Youngwer/CASA0022_Dissertation/image/neonDB table.png

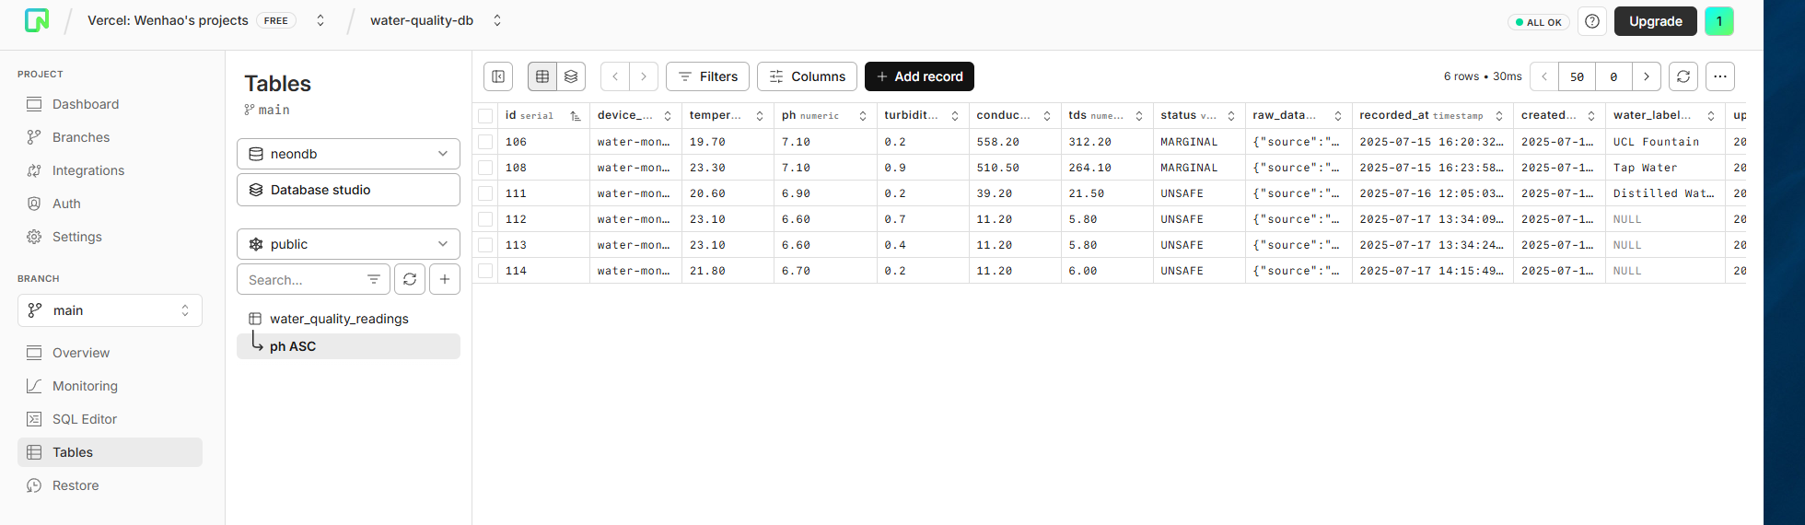
image/neonDB table.png
