Youngwer/CASA0022_Dissertation/image/pH solution.jpg

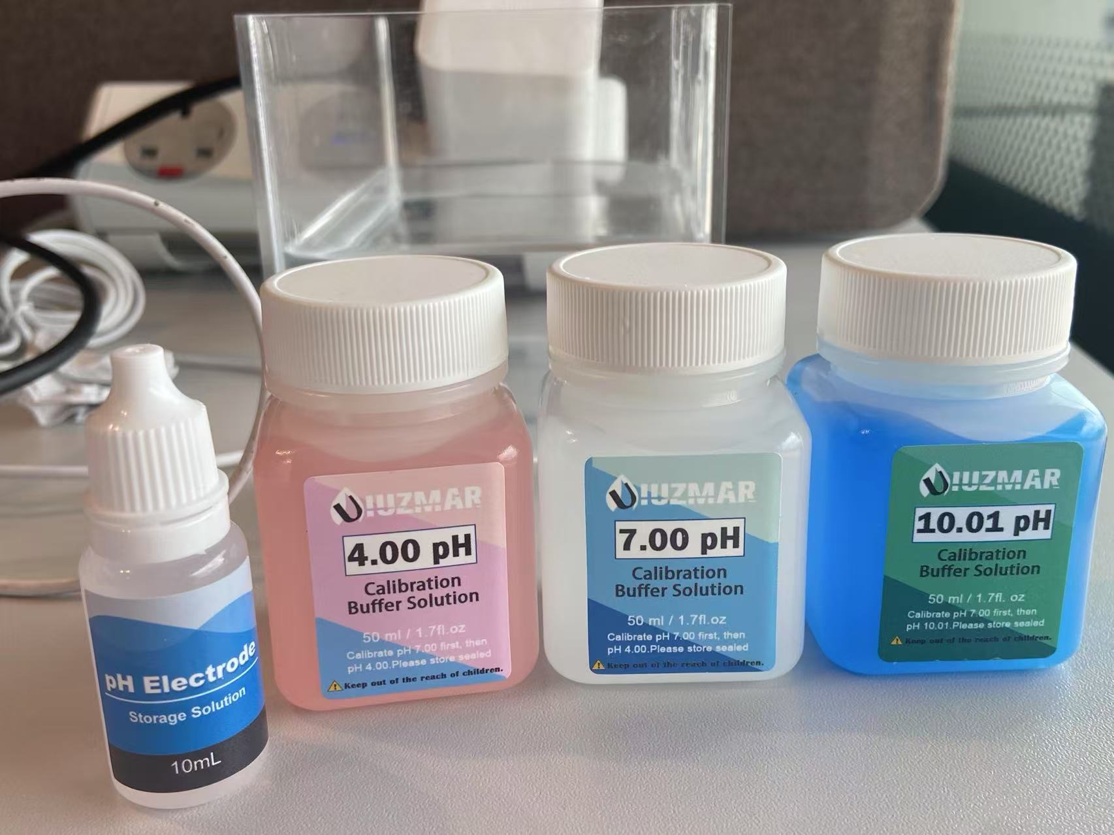
image/pH solution.jpg
