Youngwer/CASA0022_Dissertation/image/web/label choice.png

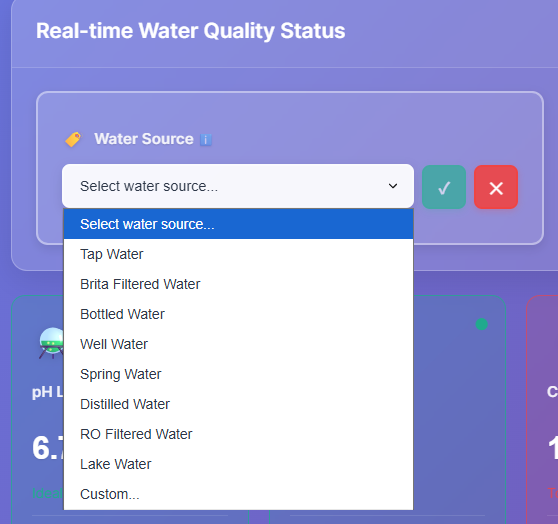
image/web/label choice.png
