Youngwer/CASA0022_Dissertation/image/Wenhao_Yang.png

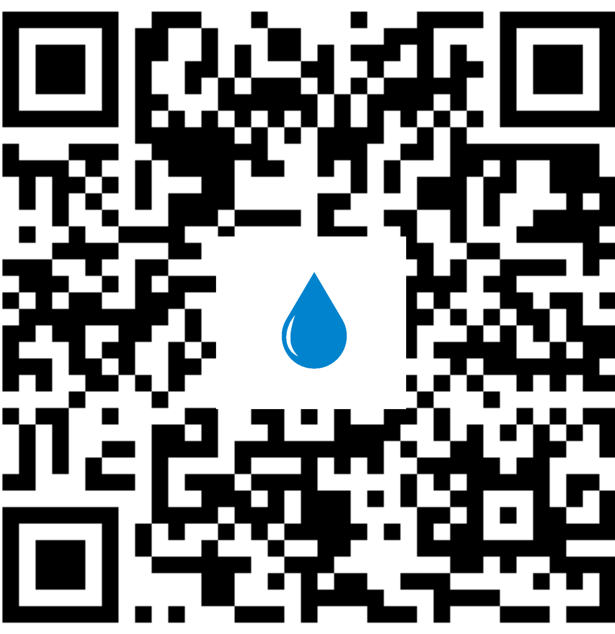
image/Wenhao_Yang.png
