Youngwer/CASA0022_Dissertation/image/Turbidity-calibration.jpg

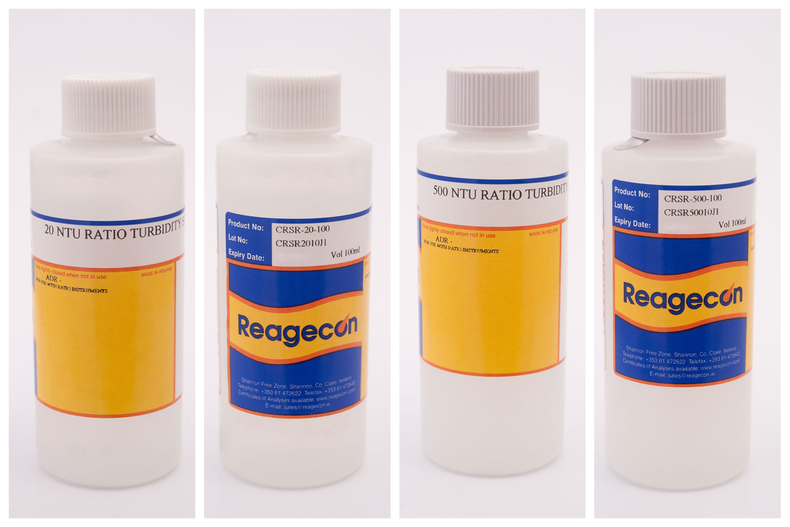
image/Turbidity-calibration.jpg
