Youngwer/CASA0022_Dissertation/image/web/history.png

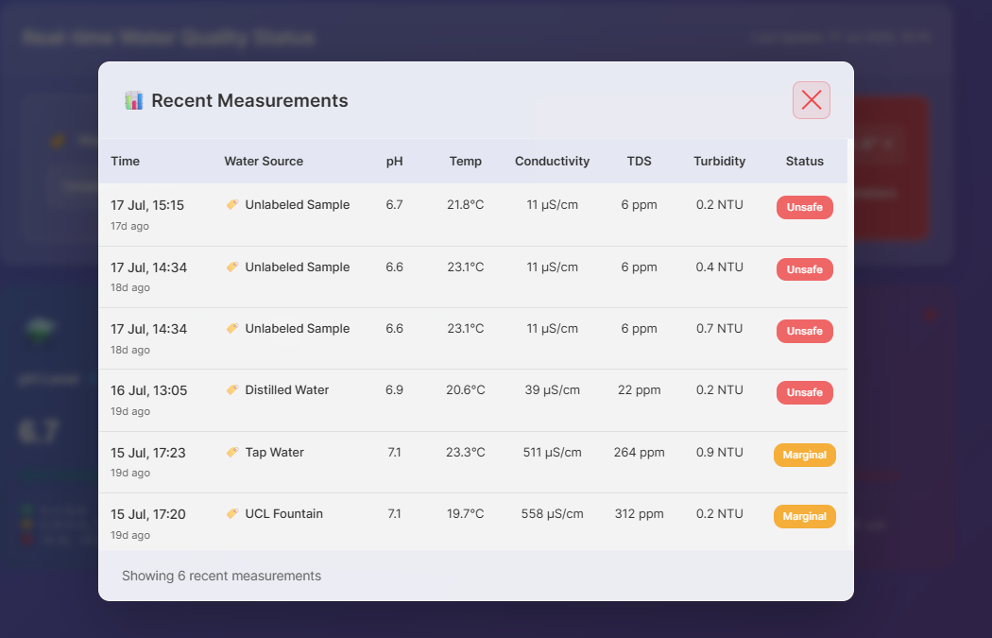
image/web/history.png
