Youngwer/CASA0022_Dissertation/Arduino/test/epaper_test/epdif.h

/**
 *  @filename   :   epdif.h
 *  @brief      :   Header file of epdif.cpp providing EPD interface functions
 *                  Users have to implement all the functions in epdif.cpp
 *  @author     :   Yehui from Waveshare
 *
 *  Copyright (C) Waveshare     August 10 2017
 *
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
 * THE SOFTWARE IS PROVIDED "AS IS", WITHOUT WARRANTY OF ANY KIND, EXPRESS OR
 * IMPLIED, INCLUDING BUT NOT LIMITED TO THE WARRANTIES OF MERCHANTABILITY,
 * FITNESS OR A PARTICULAR PURPOSE AND NONINFRINGEMENT. IN NO EVENT SHALL THE
 * AUTHORS OR COPYRIGHT HOLDERS BE LIABLE FOR ANY CLAIM, DAMAGES OR OTHER
 * LIABILITY WHETHER IN AN ACTION OF CONTRACT, TORT OR OTHERWISE, ARISING FROM,
 * OUT OF OR IN CONNECTION WITH THE SOFTWARE OR THE USE OR OTHER DEALINGS IN
 * THE SOFTWARE.
 */

#ifndef EPDIF_H
#define EPDIF_H

#include <Arduino.h>

// Pin definition
#define RST_PIN         5    // 原来是8，改为5
#define DC_PIN          6    // 原来是9，改为6
#define CS_PIN          7    // 原来是10，改为7
#define BUSY_PIN        4    // 原来是7，改为4
#define PWR_PIN         10

class EpdIf {
public:
    EpdIf(void);
    ~EpdIf(void);

    static int  IfInit(void);
    static void DigitalWrite(int pin, int value); 
    static int  DigitalRead(int pin);
    static void DelayMs(unsigned int delaytime);
    static void SpiTransfer(unsigned char data);
};

#endif
